victorjchamorro/diy-inverter/pictures/20230402_135312.jpg

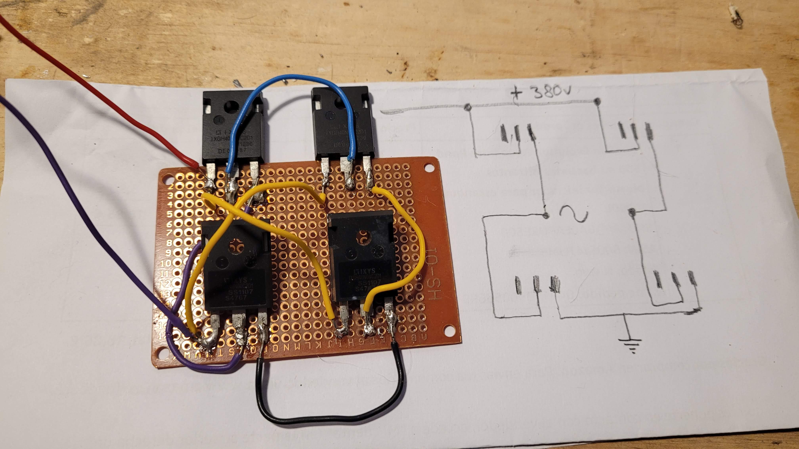
pictures/20230402_135312.jpg
