victorjchamorro/diy-inverter/pictures/20230402_135333.jpg

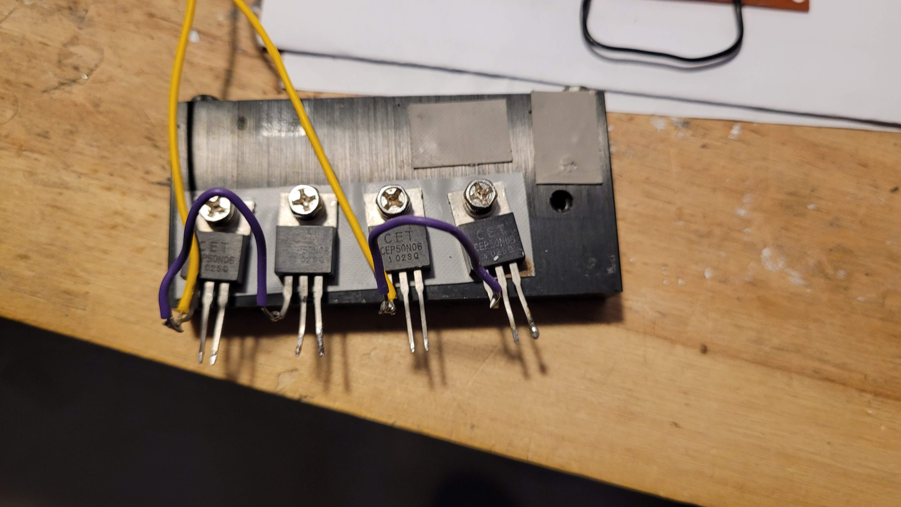
pictures/20230402_135333.jpg
