victorjchamorro/diy-inverter/pictures/20230402_135355.jpg

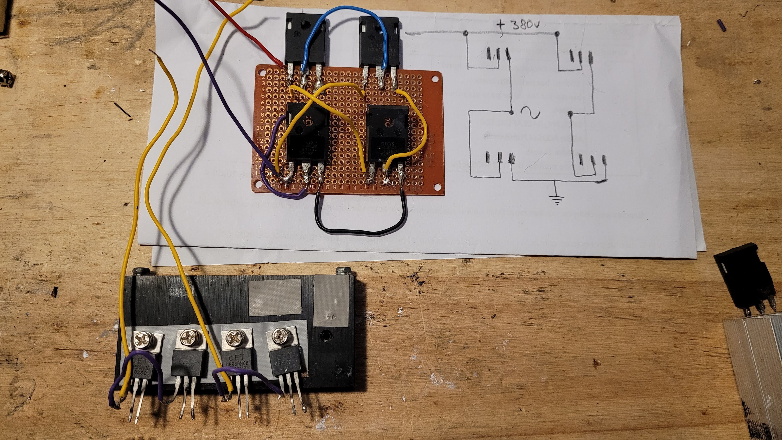
pictures/20230402_135355.jpg
