victorjchamorro/diy-inverter/pictures/20230430_162237.jpg

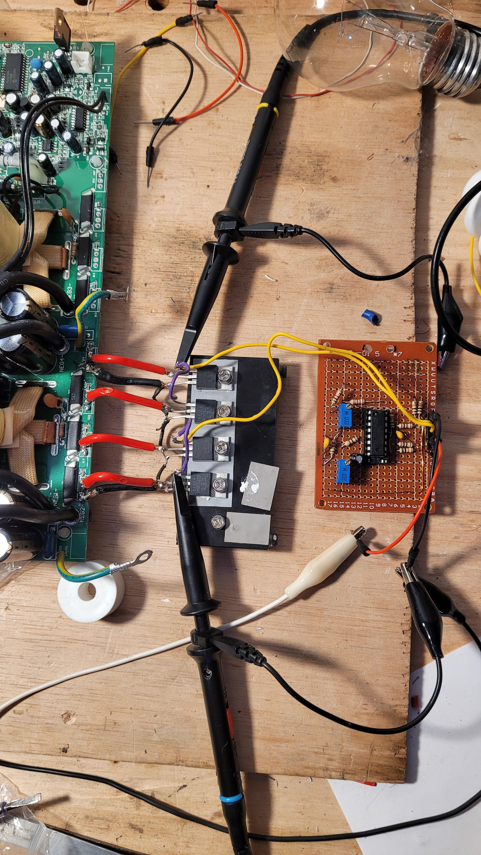
pictures/20230430_162237.jpg
