victorjchamorro/diy-inverter/pictures/20230430_162247.jpg

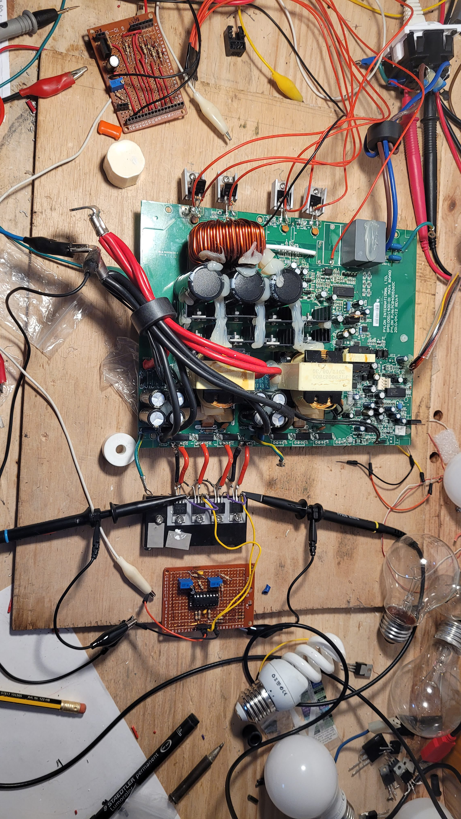
pictures/20230430_162247.jpg
