victorjchamorro/diy-inverter/pictures/20230430_162254.jpg

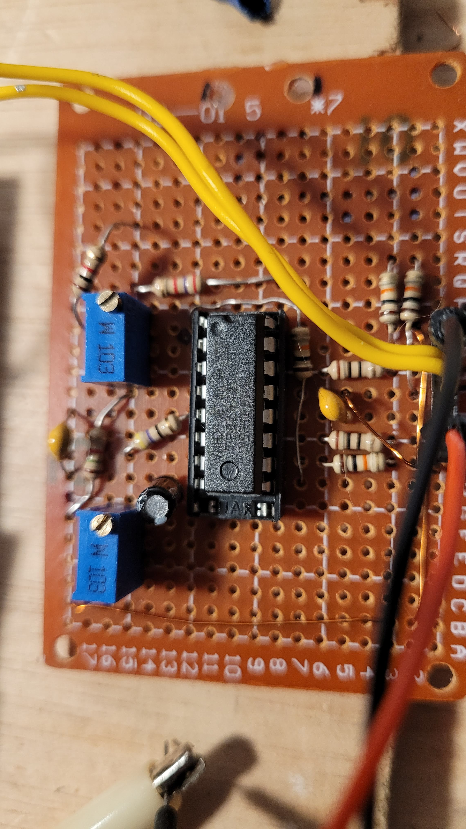
pictures/20230430_162254.jpg
