victorjchamorro/diy-inverter/pictures/20230513_143341.jpg

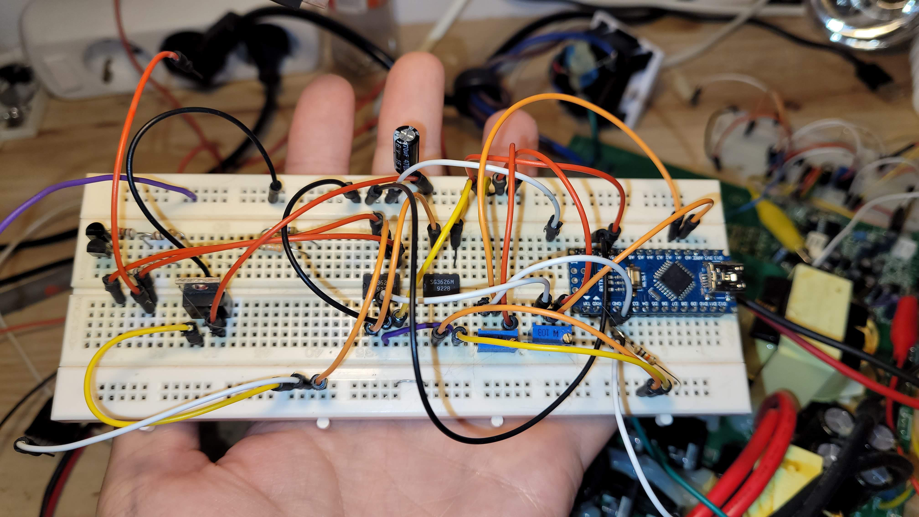
pictures/20230513_143341.jpg
