victorjchamorro/diy-inverter/pictures/20230513_143346.jpg

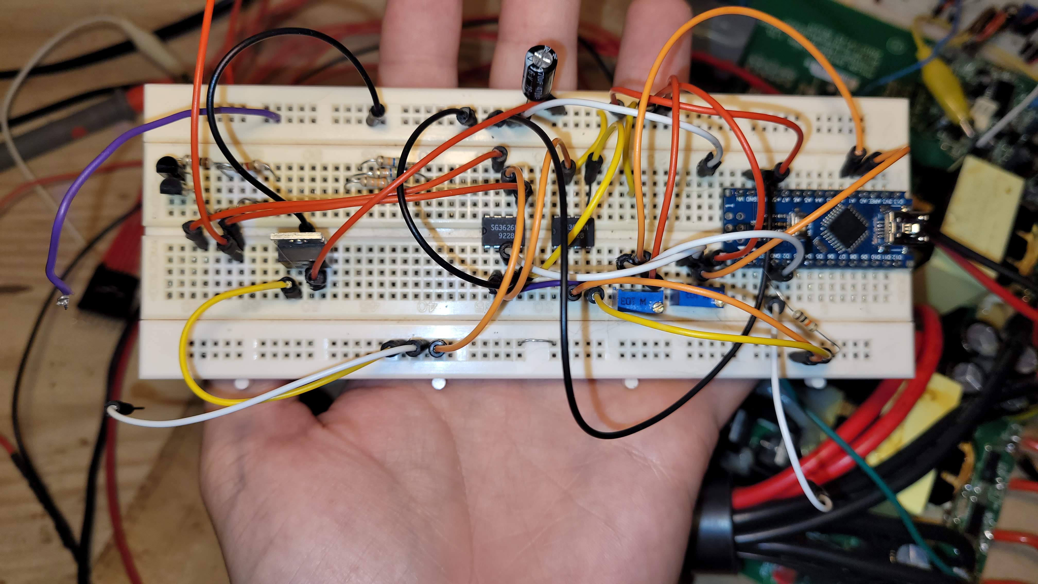
pictures/20230513_143346.jpg
