victorjchamorro/diy-inverter/pictures/20230513_143353.jpg

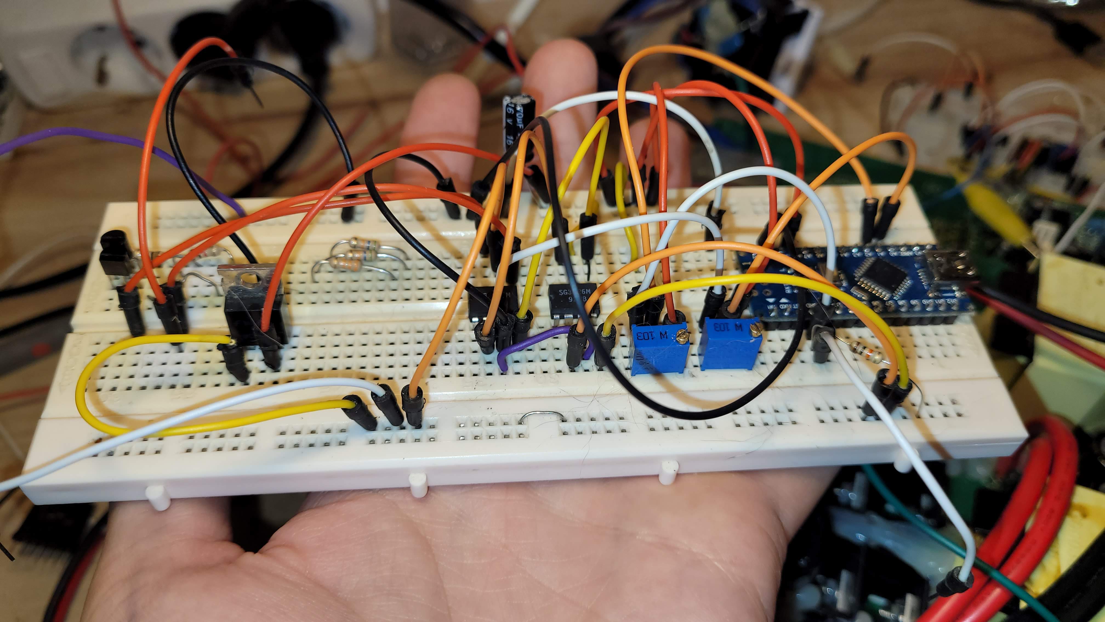
pictures/20230513_143353.jpg
