victorjchamorro/diy-inverter/pictures/20230513_143410.jpg

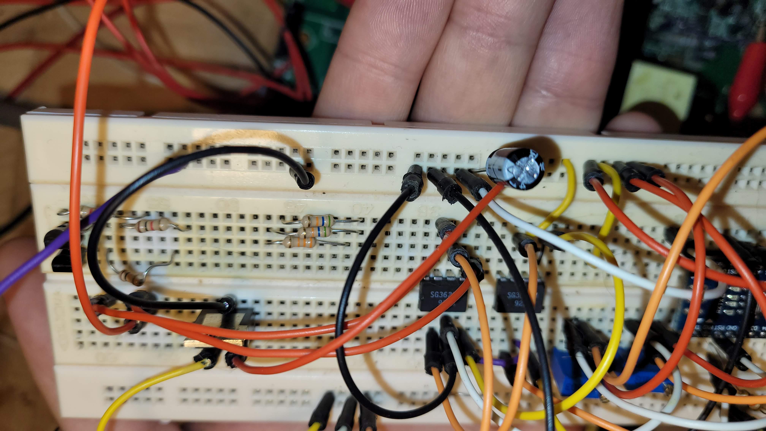
pictures/20230513_143410.jpg
