victorjchamorro/diy-inverter/pictures/20230603_192839.jpg

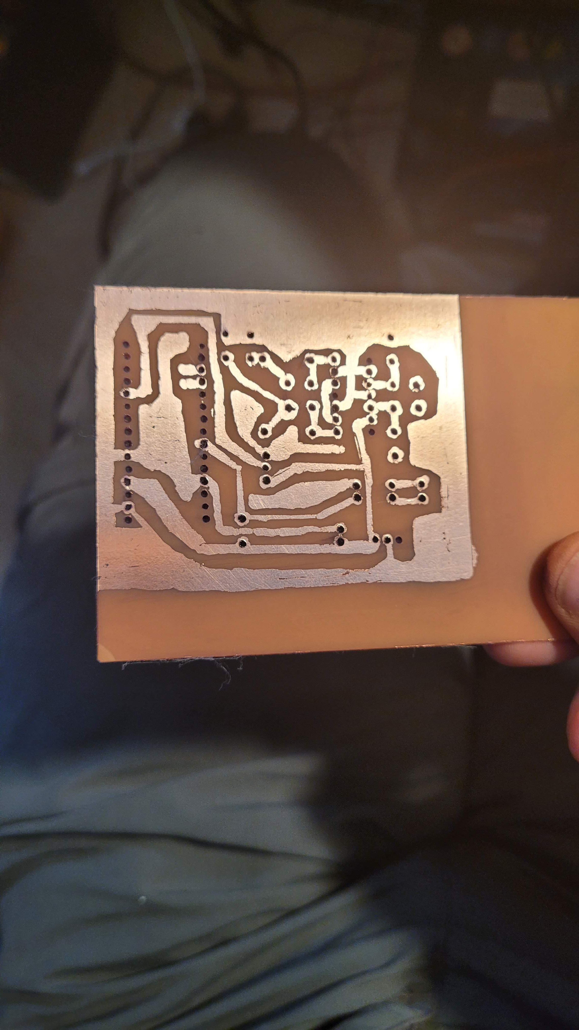
pictures/20230603_192839.jpg
