victorjchamorro/diy-inverter/pictures/20230612_205813.jpg

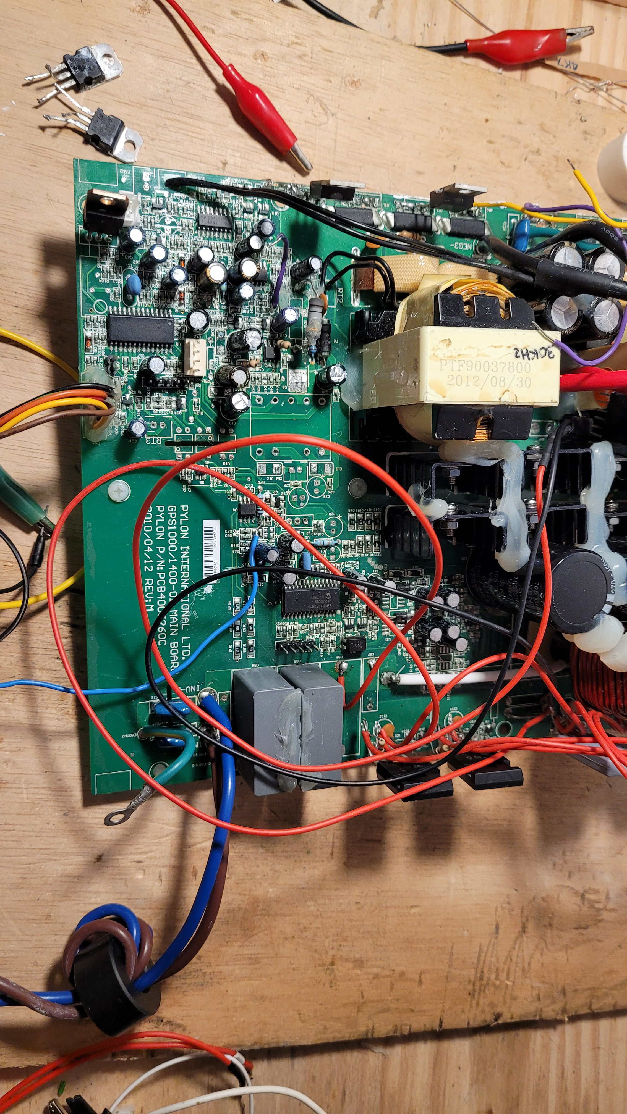
pictures/20230612_205813.jpg
