victorjchamorro/diy-inverter/pictures/20230612_205821.jpg

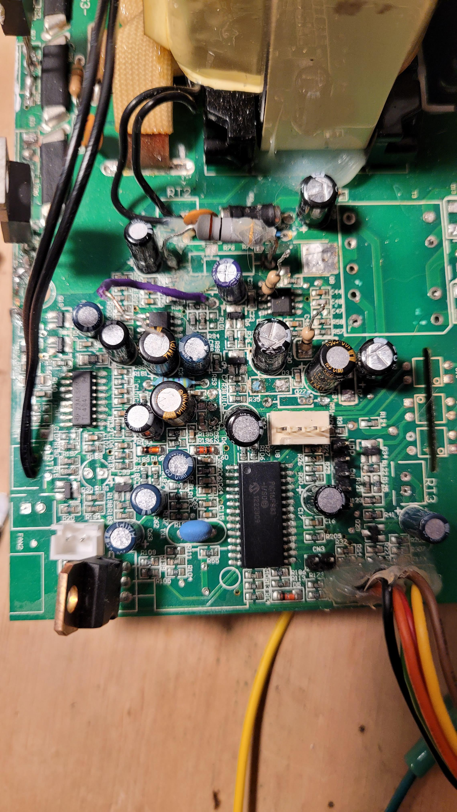
pictures/20230612_205821.jpg
