victorjchamorro/diy-inverter/pictures/20230612_205823.jpg

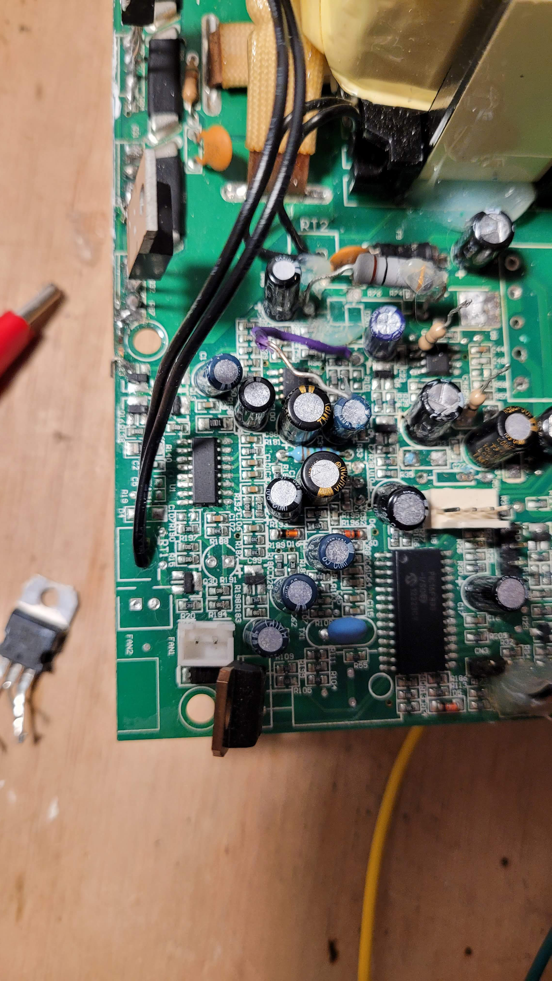
pictures/20230612_205823.jpg
