victorjchamorro/diy-inverter/pictures/20230612_205827.jpg

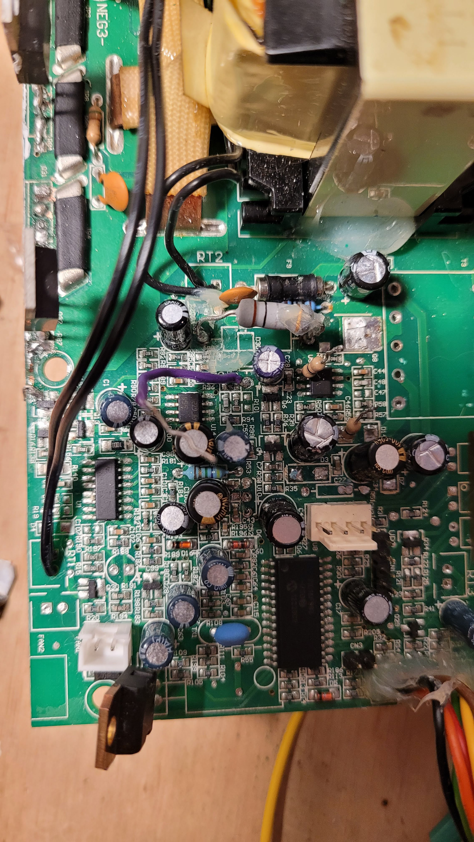
pictures/20230612_205827.jpg
