victorjchamorro/diy-inverter/pictures/20230729_141828.jpg

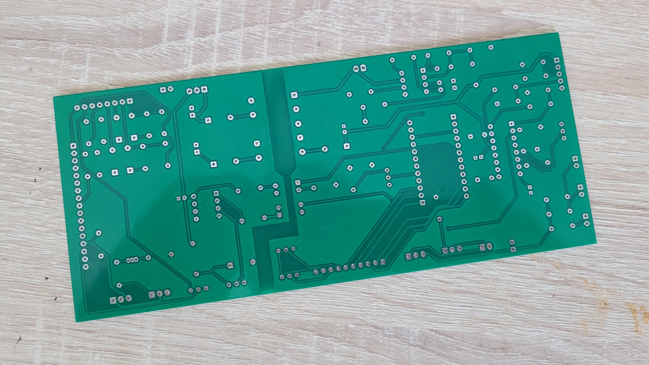
pictures/20230729_141828.jpg
