victorjchamorro/diy-inverter/pictures/20230729_141835.jpg

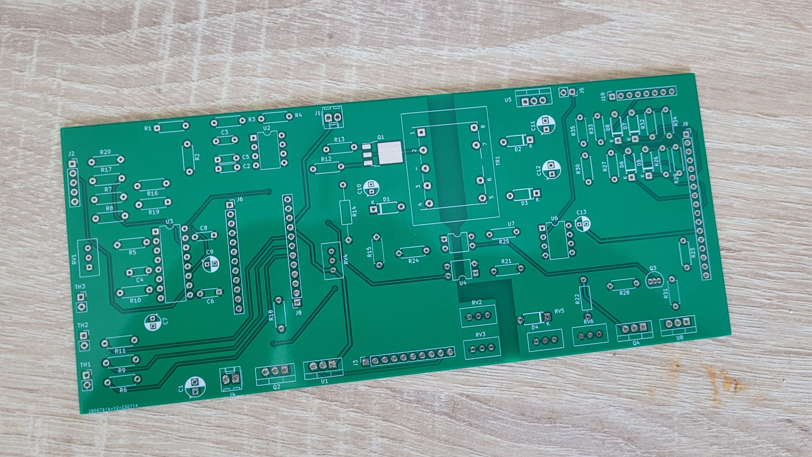
pictures/20230729_141835.jpg
