victorjchamorro/diy-inverter/pictures/20230802_221700.jpg

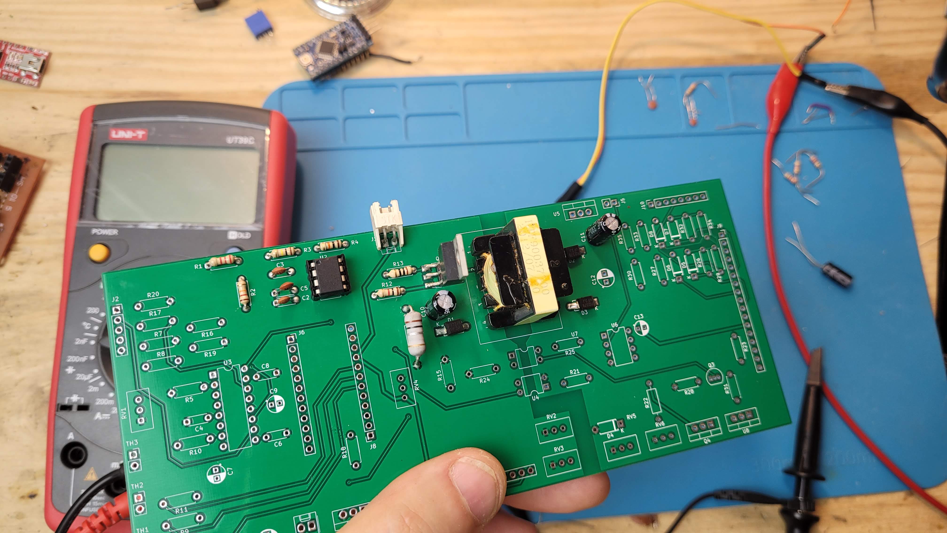
pictures/20230802_221700.jpg
